rvanil-yahoo/SmartScale/20260704_120102.jpg

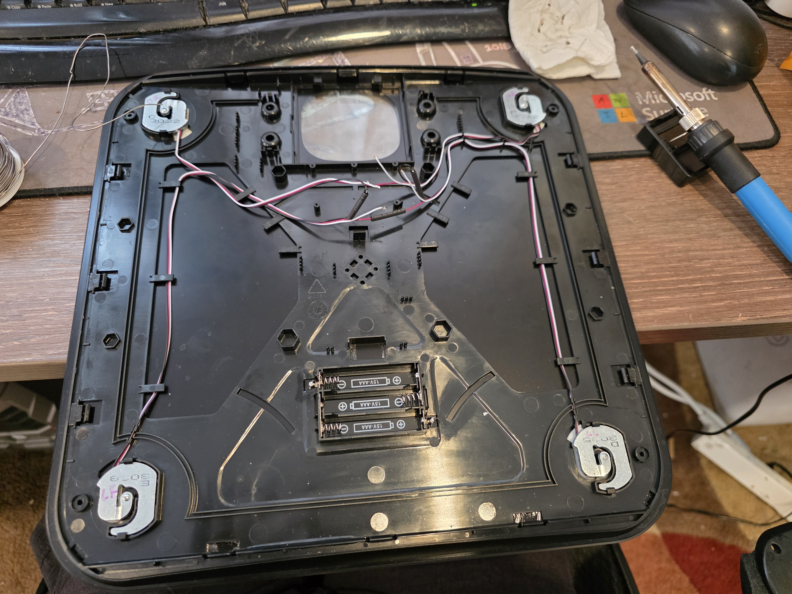
20260704_120102.jpg
