rvanil-yahoo/SmartScale/20260704_122816.jpg

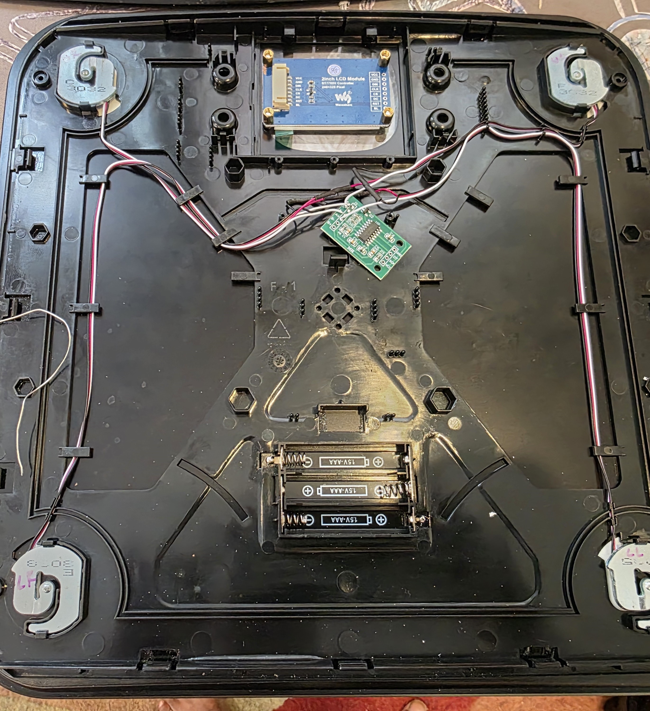
20260704_122816.jpg
