rvanil-yahoo/SmartScale/20260719_132252.jpg

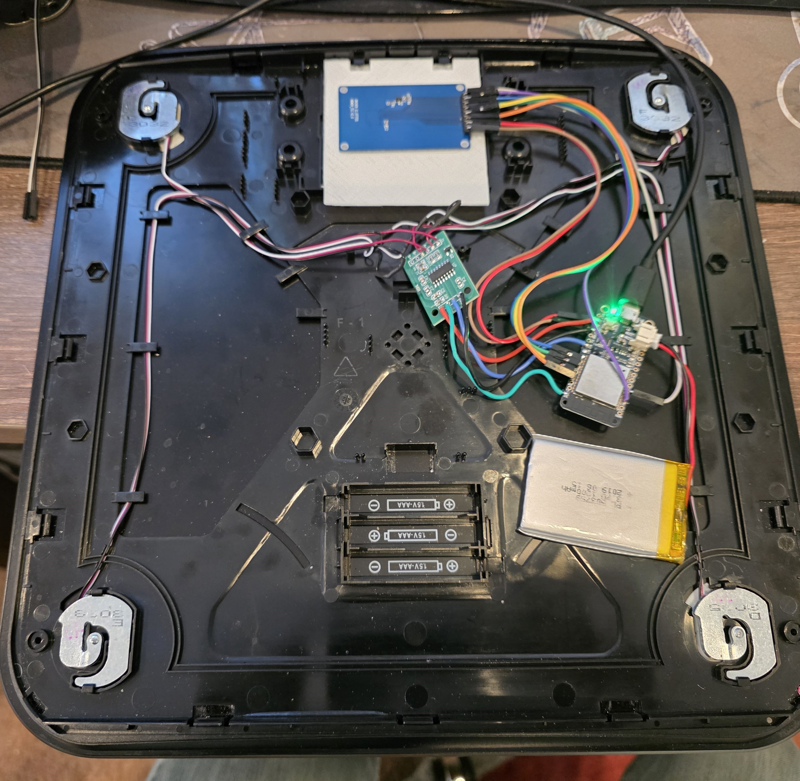
20260719_132252.jpg
