rvanil-yahoo/SmartScale/20260719_135141.jpg

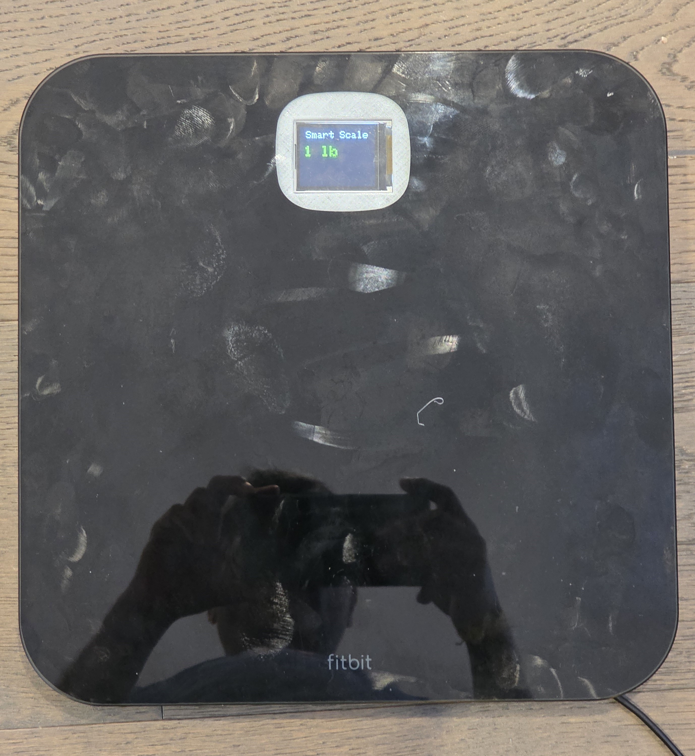
20260719_135141.jpg
